oryjkov/100pct-ptt/power/adv_1s.png

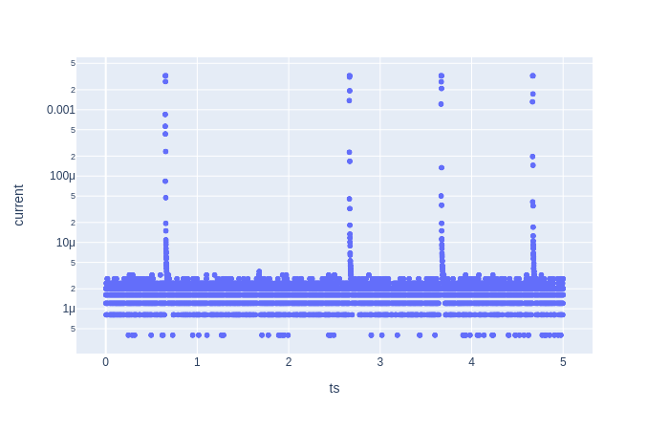
power/adv_1s.png
