oryjkov/100pct-ptt/power/adv_1s_total.png

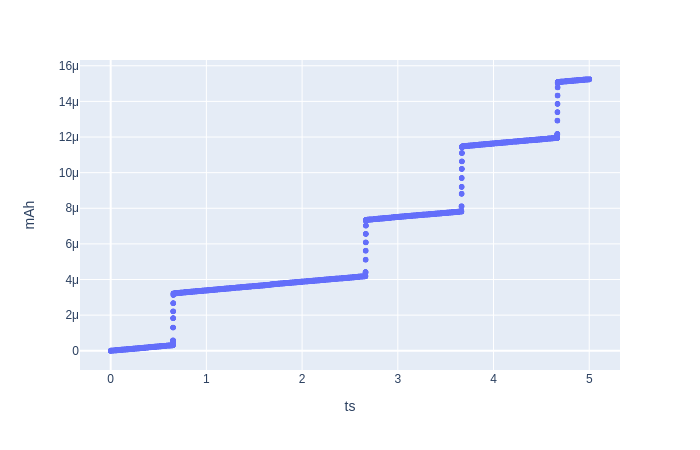
power/adv_1s_total.png
