oryjkov/100pct-ptt/power/conn_300ms.png

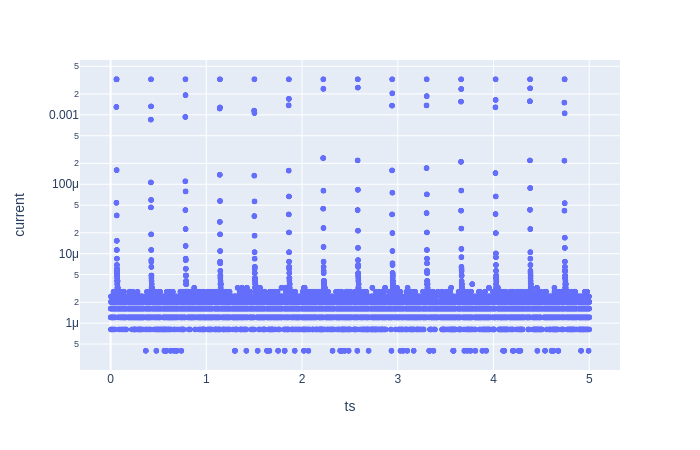
power/conn_300ms.png
